00Waz/Paxtogeddon-Reader/Images/4.jpg

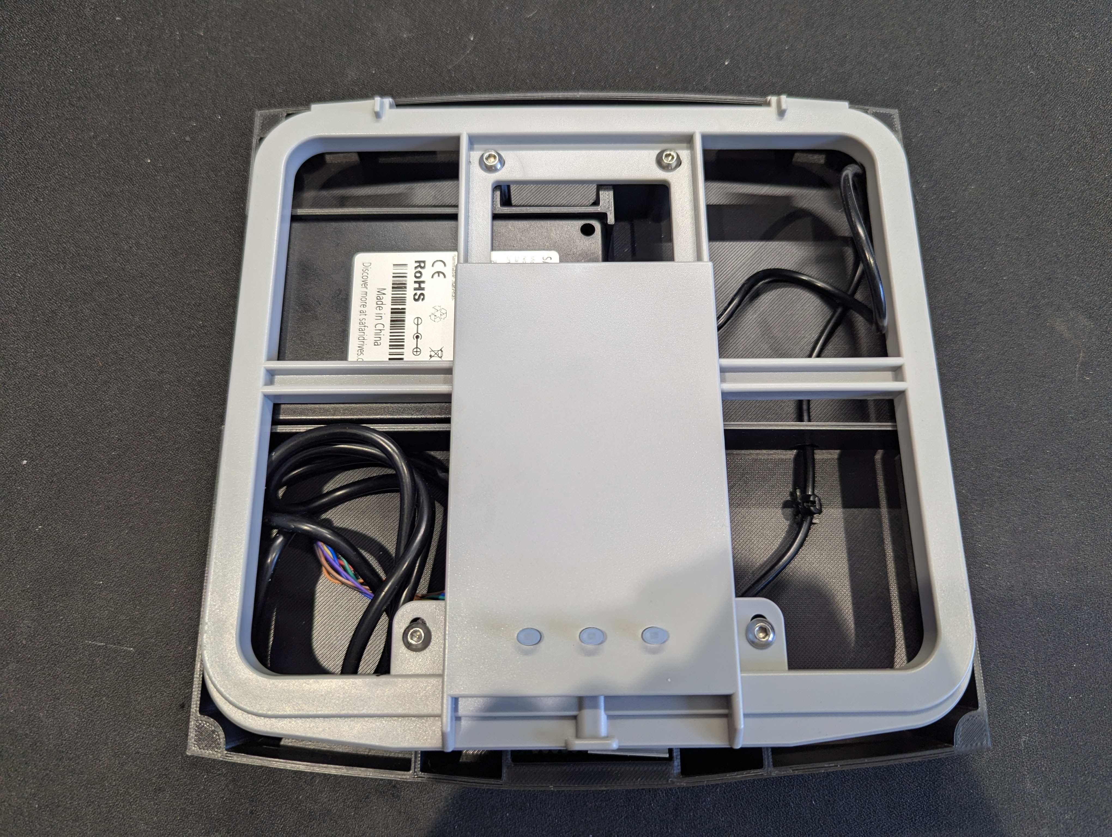
Images/4.jpg
